lekgolo167/Smart-Thermostat/include/MesgQueue.hpp

#pragma once

#include <queue>

inline std::queue<int> *global_msg_queue;

enum ThermostatMessages
{
	SAMPLE_AIR,
	RTC_UPDATE,
	GET_EPOCH,
	UPDATE_SAMPLE_PERIOD,
	SET_FILTER,
	UPDATE_SAMPLE_SUM,
	MOTION_DETECTED, // 5
	NO_MOTION,
	START_SCREEN_TIMEOUT,
	CHECK_FOR_UDP_MSG,
	UPDATE_SCHEDULE,
	START_TEMPORARY_OVERRIDE, // 10
	GET_TEMPORARY_OVERRIDE,
	GET_FORECAST,
	SEND_SERVER_TEMPERATURE,
	SEND_SERVER_STATS,
	SEND_SERVER_MOTION, // 15
	SEND_SEVER_RUNTIME,
	SEND_SERVER_FURNACE_STATE,
	OLED_ON,
	OLED_OFF,
	OLED_UPDATE, // 20
	OLED_NEXT_MENU,
	OLED_PREV_MENU,
	OLED_EDIT_MENU,
	OLED_ROTARY_CCW,
	OLED_ROTARY_CW, // 25
	CONNECT_TO_SERVER,
	CONNECT_TO_WIFI,
	DISCONNECT_WIFI,
	SELF_TEST,
	SELF_TEST_DONE
};
